shaise/OpenSky328/Software/src/storage.c

/*
    Copyright 2017 fishpepper <AT> gmail.com

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
   author: fishpepper <AT> gmail.com
*/

#include "storage.h"
#include "hal_storage.h"
#include "debug.h"
#include "wdt.h"
#include "delay.h"
#include "led.h"
#include "frsky.h"
#include "hal_defines.h"

// run time copy of persistant storage data:
EXTERNAL_MEMORY STORAGE_DESC storage;

void storage_init(void)
{
    uint8_t i;

    debug("storage: init\n");
    debug_flush();

    // init hal storage
    hal_storage_init();

    // reload data from flash
    storage_read_from_flash();

    debug("storage: loaded hoptable[] = ");
    for (i = 0; i < FRSKY_HOPTABLE_SIZE; i++)
    {
        debug_put_hex8(storage.frsky_hop_table[i]);
        debug_putc(' ');
        debug_flush();
    }
    debug_put_newline();

    debug("storage: loaded failsafe[]: ");
    for (i = 0; i < 8; i++)
    {
        debug_put_uint8(storage.fail_safe_state[i]);
        debug_putc(' ');
        debug_flush();
    }
    debug_put_newline();
}

static const uint8_t storage_default_hoptable[] =
    {0x01, 0x42, 0x83, 0xC4, 0x1A, 0x5B, 0x9C, 0xDD, 0x33, 0x74, 0xB5, 0x0B,
     0x4C, 0x8D, 0xCE, 0x24, 0x65, 0xA6, 0xE7, 0x3D, 0x7E, 0xBF, 0x15, 0x56,
     0x97, 0xD8, 0x2E, 0x6F, 0xB0, 0x06, 0x47, 0x88, 0xC9, 0x1F, 0x60, 0xA1,
     0xE2, 0x38, 0x79, 0xBA, 0x10, 0x51, 0x92, 0xD3, 0x29, 0x6A, 0xAB};

void storage_read_from_flash(void)
{
    uint8_t *storage_ptr;
    uint16_t len;
    uint8_t i;

    debug("storage: reading\n");
    debug_flush();
    storage_ptr = (uint8_t *)&storage;
    len = sizeof(storage);

    hal_storage_read(storage_ptr, len);

#ifdef FRSKY_USE_FIXED_ID
    // allow override for testing
    if (1)
    {
#else  // FRSKY_USE_FIXED_ID
    // only init with defaults when no valid storage id was found
    if (storage.version != STORAGE_VERSION_ID)
    {
#endif // FRSKY_USE_FIXED_ID
        debug("storage: init with defaults (txid 0x1668)\n");

        storage.version = STORAGE_VERSION_ID;

        // hard coded config for debugging:
        storage.frsky_txid[0] = 0x16;
        storage.frsky_txid[1] = 0x68;
        storage.frsky_freq_offset = DEFAULT_FSCAL_VALUE;

        for (i = 0; i < FRSKY_HOPTABLE_SIZE; i++)
        {
            storage.frsky_hop_table[i] = storage_default_hoptable[i];
        }

        // fill default failsafe state
        for (i = 0; i < 8; i++)
        {
            storage.fail_safe_state[i] = 150; // = 1.5 ms
        }
#ifndef RXBOARD_FRLVH
        storage.fail_safe_state[2] = 100; // channel 3 (throttle) to minimum
#endif

        // store settings
        storage_write_to_flash();
    }
}

void storage_write_to_flash(void)
{
    uint8_t *storage_ptr;
    uint16_t len;

    debug("storage: writing\n");
    debug_flush();
    storage.version = STORAGE_VERSION_ID;

    storage_ptr = (uint8_t *)&storage;
    len = sizeof(storage);

    // execute flash write:
    hal_storage_write(storage_ptr, len);
}
